LeandroBenitez12/Laberinto-BoverJR/Design 3D/2022 - Bover JR/Pololu Magnetic Encoder.SLDPRT

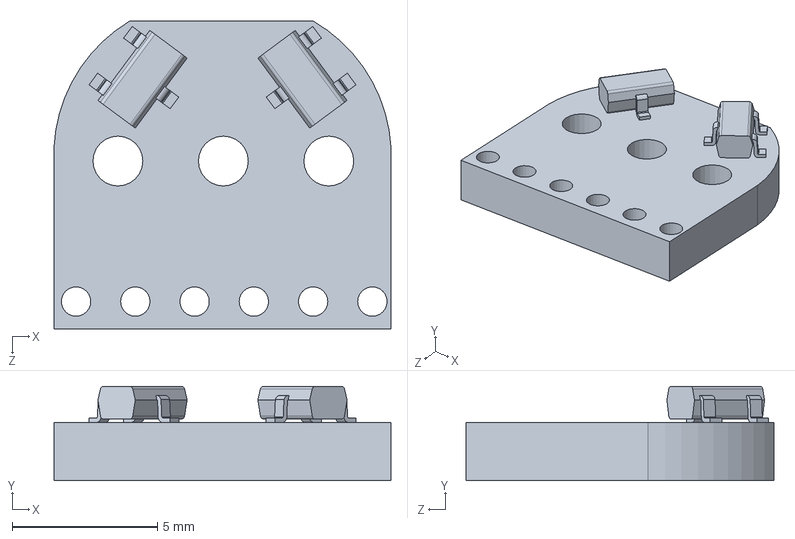
[picture p18: CAD file, 2023-09-27]
Design 3D/2022 - Bover JR/Pololu Magnetic Encoder.SLDPRT
11.6 x 3.24 x 10.6 mm
