LeandroBenitez12/Laberinto-BoverJR/Design 3D/2022 - Bover JR/Llanta_3D_V2.SLDPRT

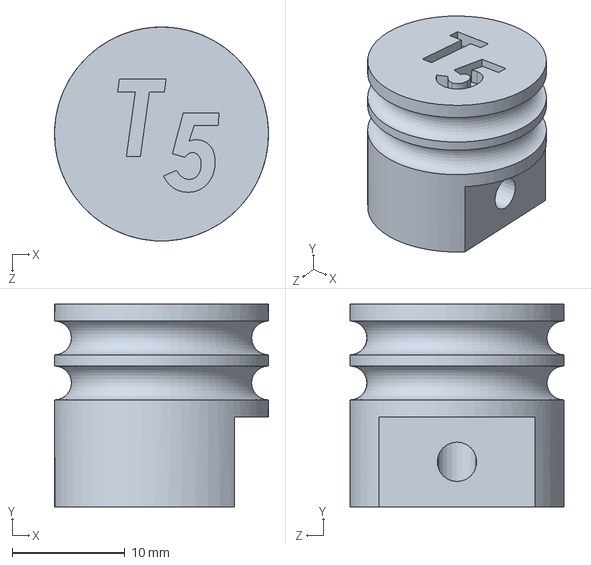
[picture p19: CAD file, 2023-09-27]
Design 3D/2022 - Bover JR/Llanta_3D_V2.SLDPRT
19.0 x 18.0 x 19.0 mm
