LeandroBenitez12/Laberinto-BoverJR/Design 3D/2022 - Bover JR/ESP_32_30Pins.SLDPRT

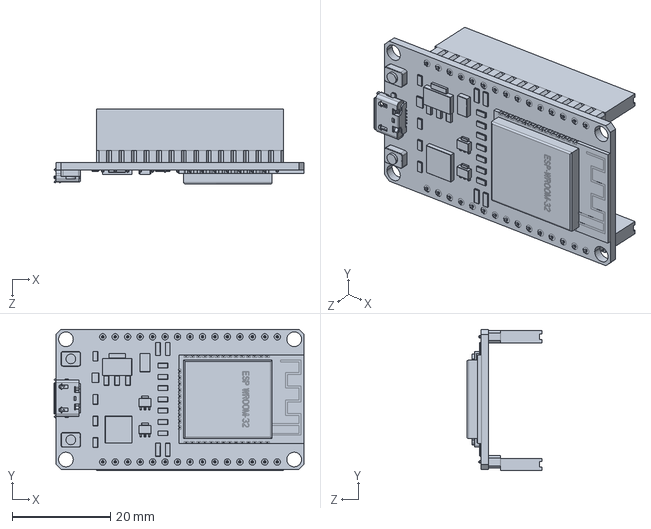
[picture p20: CAD file, 2023-09-27]
Design 3D/2022 - Bover JR/ESP_32_30Pins.SLDPRT
50.9 x 28.7 x 15.3 mm
