LeandroBenitez12/Laberinto-BoverJR/Design 3D/2022 - Bover JR/Llanta_MiniSumoV1.SLDPRT

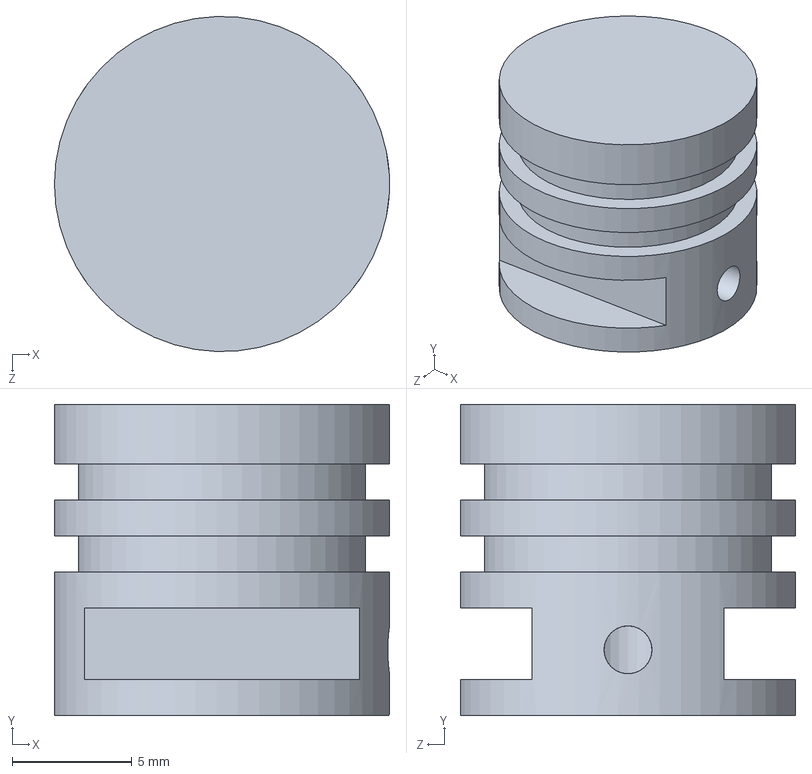
[picture p21: CAD file, 2023-09-27]
Design 3D/2022 - Bover JR/Llanta_MiniSumoV1.SLDPRT
14.0 x 13.0 x 14.0 mm
