LeandroBenitez12/Laberinto-BoverJR/Design 3D/2022 - Bover JR/SoporteSharps.SLDPRT

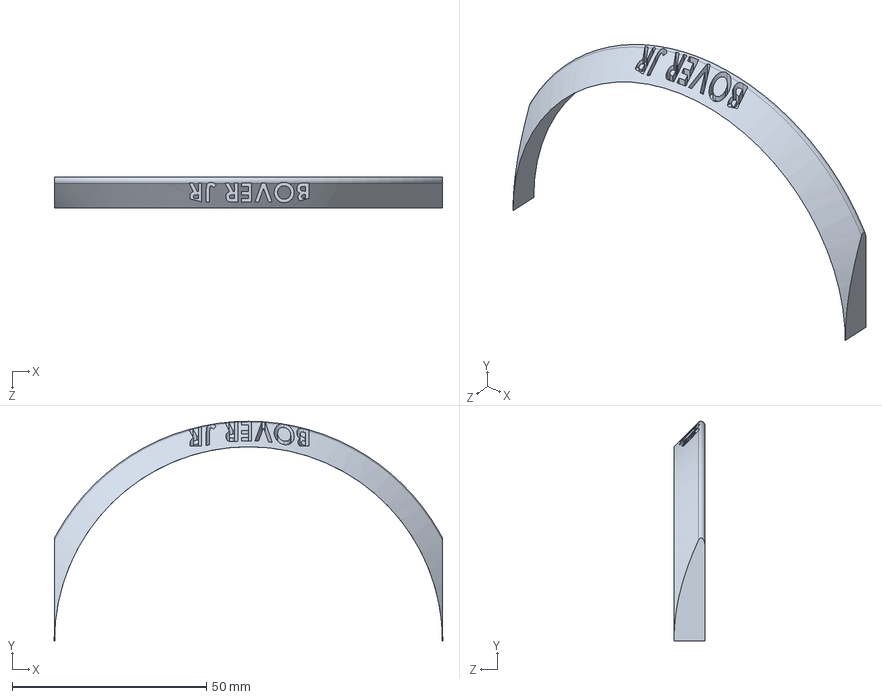
[picture p22: CAD file, 2023-09-27]
Design 3D/2022 - Bover JR/SoporteSharps.SLDPRT
100.0 x 56.6 x 8.00 mm
