LeandroBenitez12/Laberinto-BoverJR/Design 3D/2022 - Bover JR/soporte_piso.SLDPRT

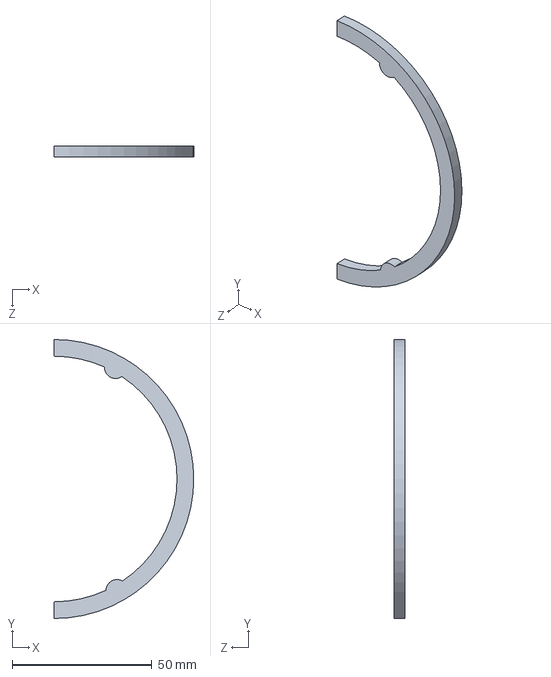
[picture p23: CAD file, 2023-09-27]
Design 3D/2022 - Bover JR/soporte_piso.SLDPRT
50.0 x 100.0 x 4.00 mm
