LeandroBenitez12/Laberinto-BoverJR/Design 3D/2022 - Bover JR/Pololu Magnetic Encoder #1523.SLDPRT

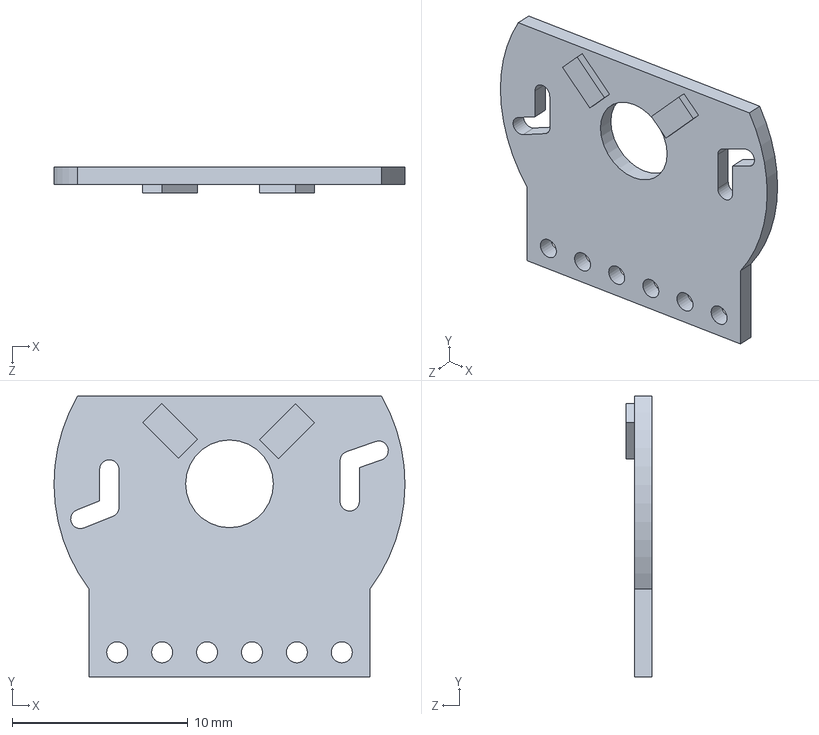
[picture p24: CAD file, 2023-09-27]
Design 3D/2022 - Bover JR/Pololu Magnetic Encoder #1523.SLDPRT
20.0 x 16.0 x 1.50 mm
