LeandroBenitez12/Laberinto-BoverJR/Software/Librerias/EngineController/Examples/Example_Driver_DRV8825/Example_Driver_DRV8825.ino

#include <EngineController.h>

#define PIN_RIGHT_ENGINE_IN1 21
#define PIN_RIGHT_ENGINE_IN2 19
#define PIN_LEFT_ENGINE_IN1 22
#define PIN_LEFT_ENGINE_IN2 23
#define PWM_CHANNEL_RIGHT_IN1 1
#define PWM_CHANNEL_RIGHT_IN2 2
#define PWM_CHANNEL_LEFT_IN1 3
#define PWM_CHANNEL_LEFT_IN2 4
IEngine *rightEngine = new Driver_DRV8825(PIN_RIGHT_ENGINE_IN1, PIN_RIGHT_ENGINE_IN2, PWM_CHANNEL_RIGHT_IN1, PWM_CHANNEL_RIGHT_IN2);
IEngine *leftEngine = new Driver_DRV8825(PIN_LEFT_ENGINE_IN1, PIN_LEFT_ENGINE_IN2, PWM_CHANNEL_LEFT_IN1, PWM_CHANNEL_LEFT_IN2);
EngineController *robot = new EngineController(rightEngine, leftEngine);
void setup()
{
}

void loop()
{
    robot->Forward(200);
    delay(3000);
    robot->Backward(200);
    delay(3000);
    robot->Left(200);
    delay(3000);
    robot->Right(200);
    delay(3000);
    robot->Stop();
    delay(3000);
}
